belief-in-magic/the-peoples-horn/firmware/main/util.h

#pragma once

#include "wav.h"

extern uint16_t tos(uint8_t* bytes);
extern uint32_t tol(uint8_t* bytes);
extern uint16_t tos(char* bytes);
extern uint32_t tol(char* bytes);
extern uint32_t min(uint32_t a, uint32_t b);
extern uint32_t max(uint32_t a, uint32_t b);
